MrBuggySan/UofC_SolarCar_MPPT/src/Helianthus21_modes.h

/*
 * Helianthus21_modes.h
 *
 *  Created on: May 2, 2015
 *      Author: Andrei
 */


#ifndef HELIANTHUS2_MODES_H_
#define HELIANTHUS2_MODES_H_

void IV_trace(void);
void Boost_Efficiency(void);
void track_MPP_dynamic(void);
void track_MPP_static(void);

#endif /* HELIANTHUS2_MODES_H_ */
